whowechina/geki_pico/Production/3DPrint/geki_pico_lever_rotator_5mm.stl

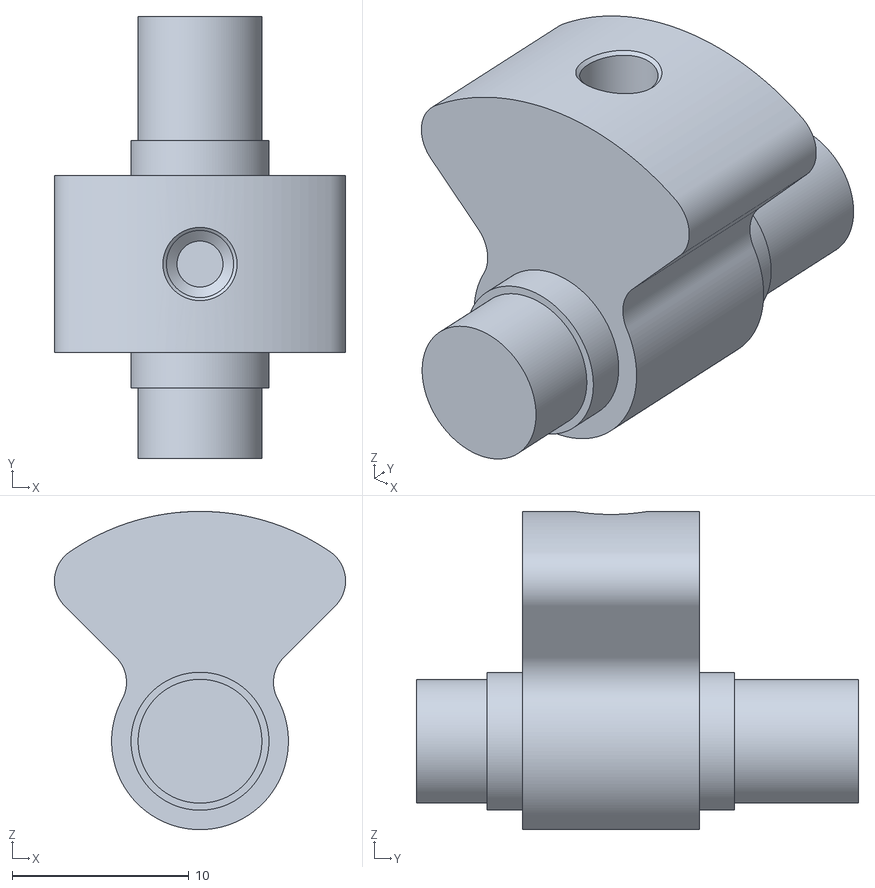
[picture p38: CAD file, 2024-10-14]
Production/3DPrint/geki_pico_lever_rotator_5mm.stl
16.5 x 25.0 x 18.0
