whowechina/geki_pico/PCB/main/3dmodels/SKPMAM.STEP

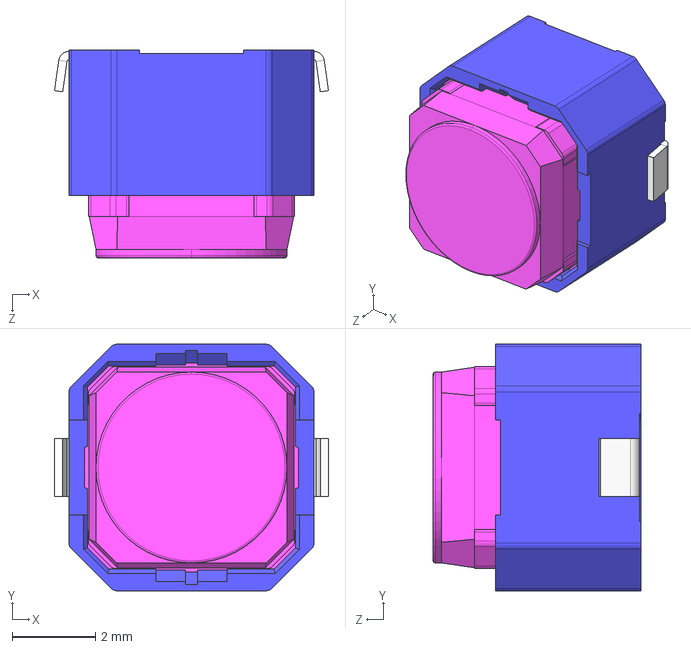
[picture p39: CAD file, 2023-09-29]
PCB/main/3dmodels/SKPMAM.STEP
6.60 x 5.94 x 5.00 mm
