whowechina/geki_pico/PCB/main/3dmodels/mpr121_breakout_v13.stl

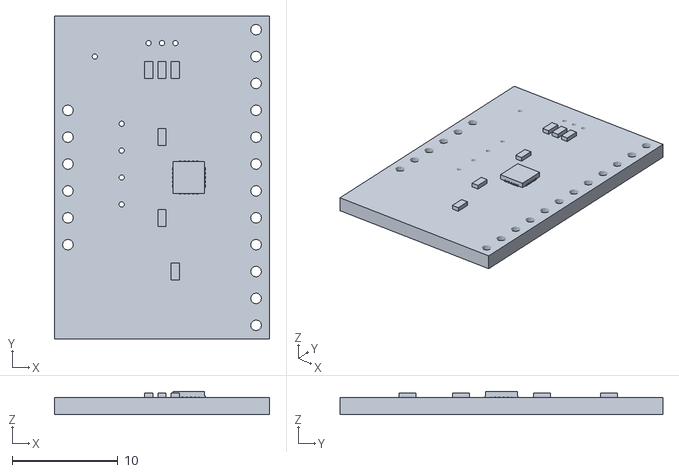
[picture p40: CAD file, 2023-09-29]
PCB/main/3dmodels/mpr121_breakout_v13.stl
20.3 x 30.5 x 2.20
