whowechina/geki_pico/Production/3DPrint/geki_pico_lever_fixer.stl

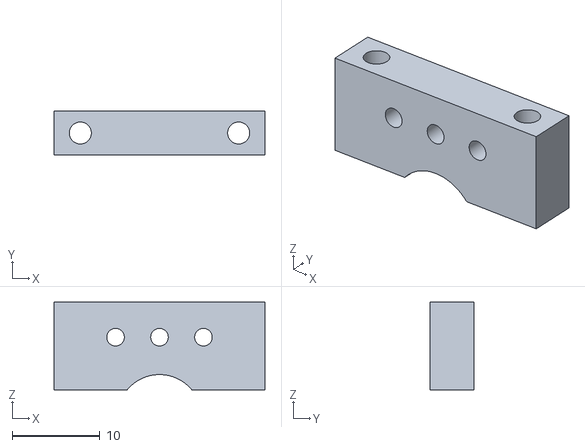
[picture p41: CAD file, 2024-10-14]
Production/3DPrint/geki_pico_lever_fixer.stl
24.0 x 5.00 x 10.0
