whowechina/geki_pico/Production/3DPrint/geki_pico_support_2_tof_no_cover.stl

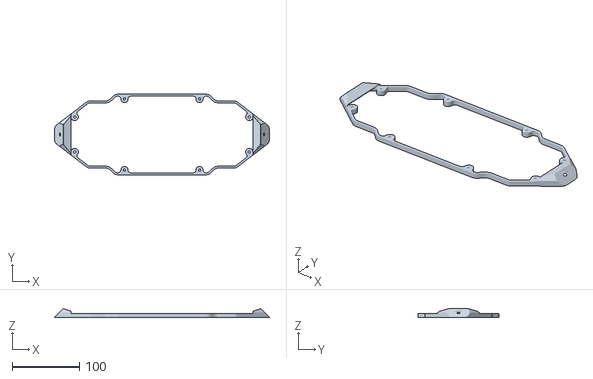
[picture p43: CAD file, 2024-09-18]
Production/3DPrint/geki_pico_support_2_tof_no_cover.stl
320.0 x 120.0 x 12.9
