whowechina/geki_pico/PCB/main/3dmodels/chu_keypad_lgp.step

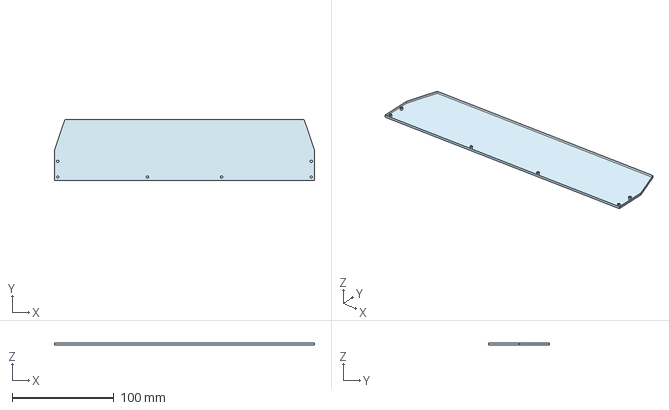
[picture p44: CAD file, 2023-09-29]
PCB/main/3dmodels/chu_keypad_lgp.step
256.0 x 60.0 x 2.00 mm
