whowechina/geki_pico/Production/3DPrint/geki_pico_button_aux.stl

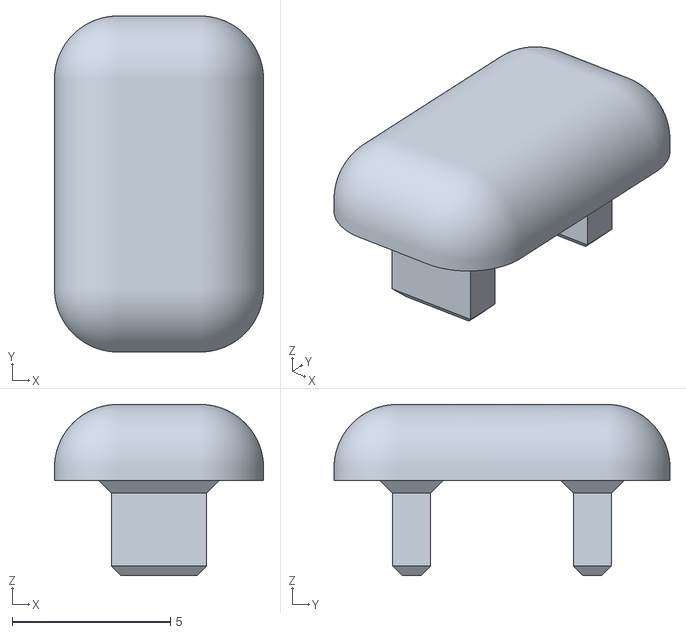
[picture p45: CAD file, 2024-09-17]
Production/3DPrint/geki_pico_button_aux.stl
6.60 x 10.6 x 5.40
