whowechina/geki_pico/PCB/main/3dmodels/Slider.step

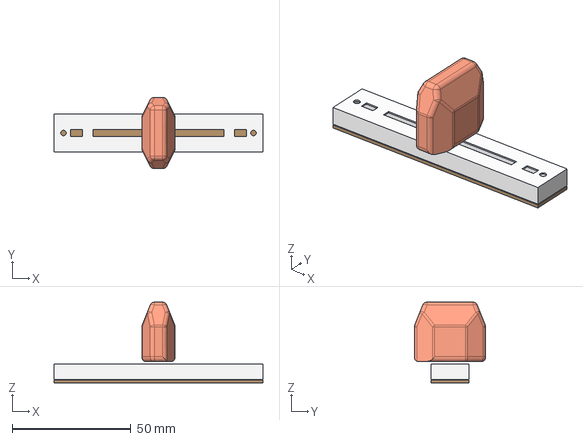
[picture p46: CAD file, 2023-09-29]
PCB/main/3dmodels/Slider.step
88.0 x 30.0 x 34.0 mm
