whowechina/geki_pico/PCB/main/3dmodels/Magnetic Pogo Connector 5 Pin (Type 3).STEP

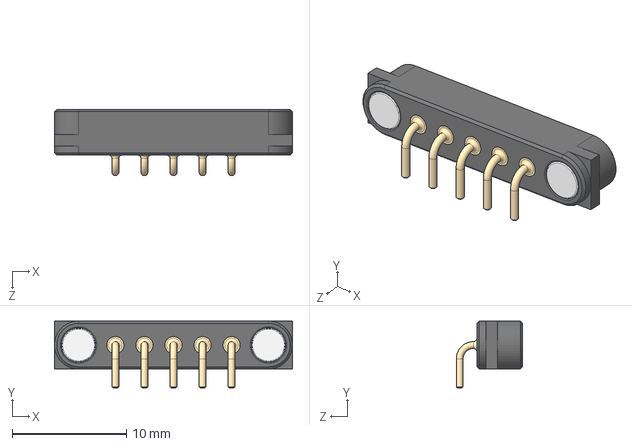
[picture p47: CAD file, 2023-09-29]
PCB/main/3dmodels/Magnetic Pogo Connector 5 Pin (Type 3).STEP
20.8 x 5.85 x 5.80 mm
