whowechina/geki_pico/Production/3DPrint/geki_pico_lever_base.stl

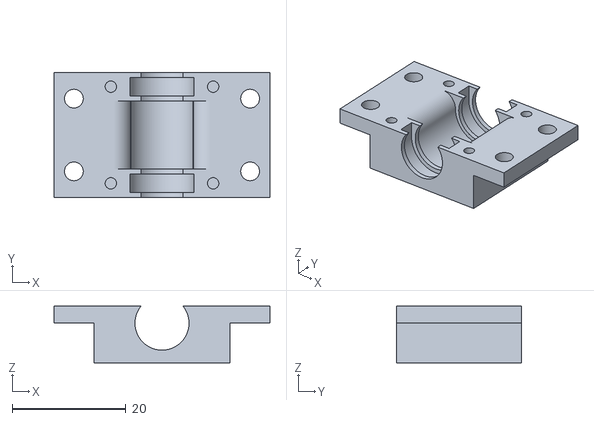
[picture p48: CAD file, 2024-09-17]
Production/3DPrint/geki_pico_lever_base.stl
38.0 x 22.0 x 10.0
