whowechina/geki_pico/PCB/main/3dmodels/gp2y0e03.3mf

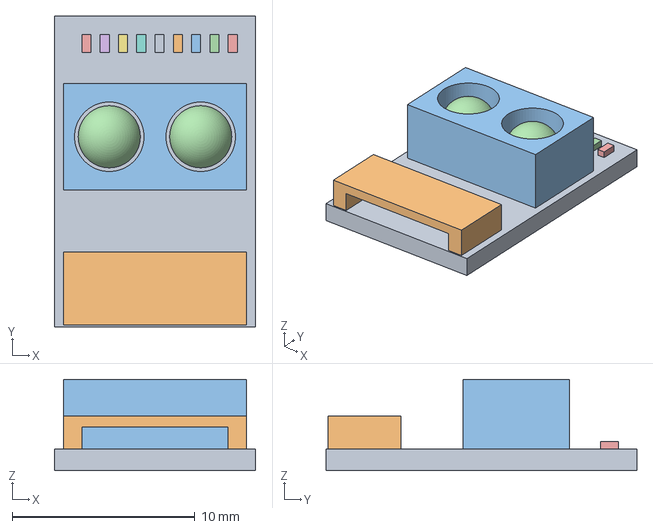
[picture p50: CAD file, 2023-09-29]
PCB/main/3dmodels/gp2y0e03.3mf
11.0 x 17.0 x 5.00 mm
