whowechina/geki_pico/PCB/main/3dmodels/Magnetic Pogo Connector 5 Pin (M) - 副本.STEP

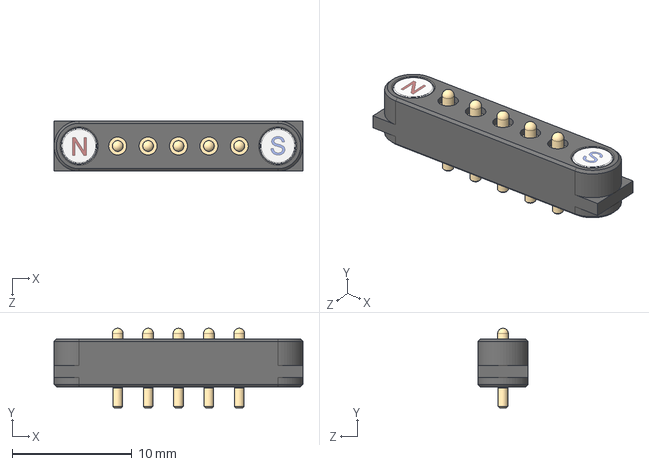
[picture p51: CAD file, 2023-09-29]
PCB/main/3dmodels/Magnetic Pogo Connector 5 Pin (M) - 副本.STEP
20.8 x 6.65 x 4.20 mm
