whowechina/geki_pico/PCB/main/3dmodels/EVQ-P1D05M.stp

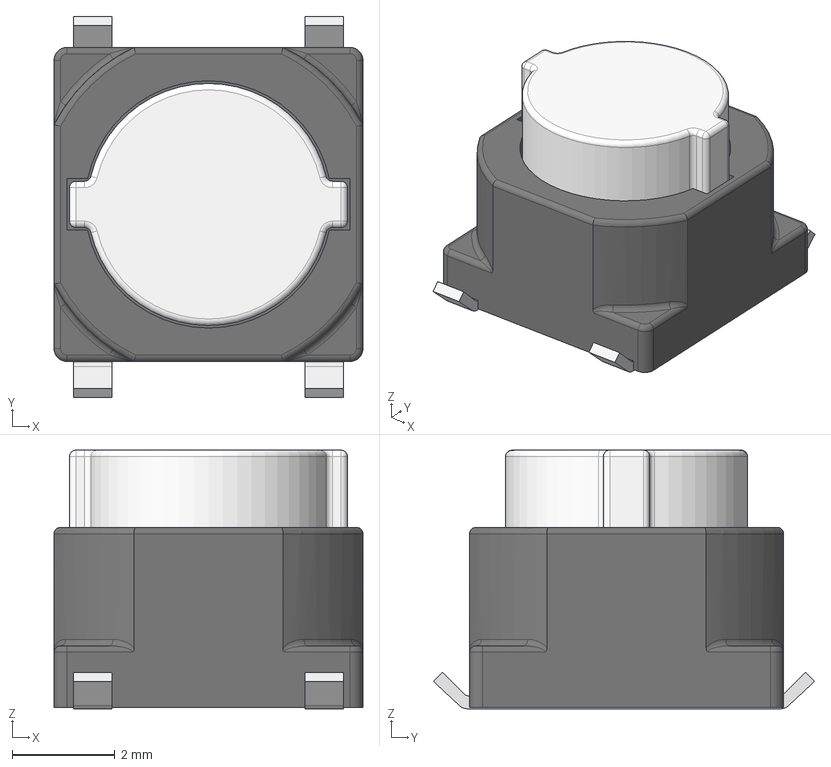
[picture p52: CAD file, 2023-09-29]
PCB/main/3dmodels/EVQ-P1D05M.stp
6.00 x 7.40 x 5.03 mm
