whowechina/geki_pico/PCB/main/3dmodels/keypad_lgp.3mf

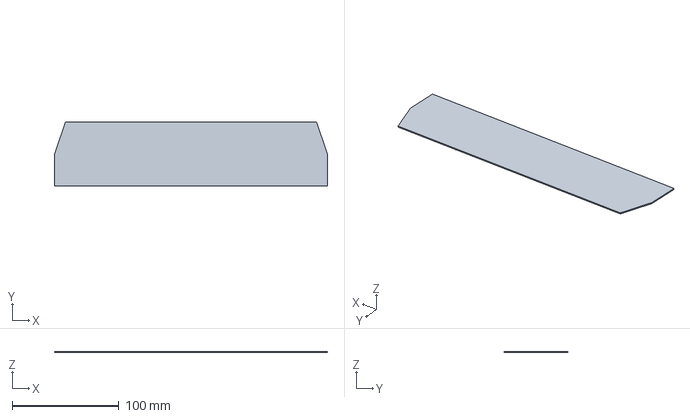
[picture p54: CAD file, 2023-09-29]
PCB/main/3dmodels/keypad_lgp.3mf
256.0 x 60.0 x 1.00 mm
