whowechina/geki_pico/firmware/src/wad_on_wav.h

const uint8_t wad_on[] = {189 , 9 , 0 , 0 , 128,126,127,127,127,127,126,127,126,126,127,126,127,127,127,124,123,124,122,124,126,126,123,125,124,125,124,124,125,123,123,123,122,123,123,124,124,123,122,120,121,121,121,122,120,121,121,121,120,120,
119,119,119,118,118,118,119,119,119,119,119,119,119,119,119,118,118,119,119,118,119,119,119,119,120,120,119,120,118,121,120,119,121,120,121,121,122,122,121,122,122,120,121,122,124,123,120,121,122,122,
122,121,121,121,121,120,120,119,119,121,122,128,119,132,129,128,130,127,124,124,126,137,127,118,124,126,130,122,129,125,125,120,122,120,126,127,124,127,130,129,129,130,132,131,129,129,134,134,136,127,
127,123,127,127,127,123,125,126,122,123,126,128,125,125,126,128,126,126,127,126,126,126,126,126,126,128,122,120,116,121,123,124,116,128,128,121,119,121,115,117,119,117,121,120,124,120,113,114,111,107,
109,112,110,108,110,108,104,103,103,101,102,101,102,99,99,99,98,98,97,97,97,96,97,95,96,94,95,93,94,93,93,92,92,92,92,92,92,92,92,91,90,92,91,91,91,90,92,90,92,92,
93,93,93,92,93,93,94,94,94,94,95,96,97,97,97,97,98,98,98,98,100,101,100,100,101,101,103,104,103,105,104,105,105,108,108,109,109,110,111,112,112,113,114,116,117,116,119,119,121,121,
123,123,124,125,126,126,128,130,131,131,133,131,133,134,136,137,137,137,136,149,150,144,140,145,153,147,143,149,149,150,152,155,154,153,152,156,154,159,159,161,160,162,162,163,163,164,165,166,166,166,
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
129,128,129,130,131,131,131,130,130,131,133,134,131,132,133,133,132,133,133,133,133,134,133,133,135,134,134,134,135,134,134,135,136,134,135,135,136,135,131,132,132,135,136,136,136,134,134,134,136,135,
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
