whowechina/geki_pico/firmware/src/wad_off_wav.h

const uint8_t wad_off[] ={159 , 4 , 0 , 0 , 119,135,131,118,123,133,131,128,118,134,124,125,125,124,138,124,125,132,118,139,119,136,130,114,139,128,124,135,129,122,125,127,134,123,140,114,134,127,118,141,124,129,119,134,117,138,127,119,141,111,
131,134,122,128,127,124,138,119,143,120,122,143,113,141,131,121,126,111,148,119,136,125,119,129,119,138,123,135,128,115,133,125,141,123,123,136,100,148,120,130,139,120,124,128,121,136,120,137,119,123,
127,123,141,121,129,115,130,130,129,133,127,121,127,122,136,130,117,129,112,128,124,135,133,112,141,114,133,124,123,135,118,138,111,126,131,121,138,116,119,133,125,134,132,116,137,104,139,125,126,130,
114,133,130,125,134,112,134,120,124,149,93,148,112,132,140,94,154,109,127,151,89,155,120,117,158,87,144,124,111,158,102,141,117,121,138,105,159,112,125,124,125,121,127,132,128,121,124,110,130,137,
122,142,122,114,130,122,127,128,121,137,103,135,122,116,135,115,146,110,138,129,110,151,113,122,128,109,145,106,139,131,97,146,103,131,126,110,150,102,131,122,133,140,105,105,147,101,133,142,100,150,
88,139,126,111,164,90,137,120,119,138,125,116,118,140,124,128,128,109,132,117,139,118,111,146,121,129,116,118,126,120,138,121,103,127,117,136,127,115,138,116,121,128,121,139,128,112,124,140,114,152,
110,126,121,122,134,121,145,102,120,141,103,160,106,122,138,103,160,92,162,109,103,140,116,127,136,100,153,100,126,142,100,159,104,109,152,82,161,105,136,127,97,161,66,173,124,114,136,93,152,105,
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
129,129,129,129,129,128,128,128,128,128,128,128,128,128,128,128,128,128,127,127,127,127,127,127,127,127,127,127,127,127,127,127,127,};
