whowechina/geki_pico/firmware/src/button.c

/*
 * Controller Buttons
 * WHowe <github.com/whowechina>
 * 
 */

#include "button.h"

#include <stdint.h>
#include <stdbool.h>
#include <string.h>

#include "hardware/gpio.h"
#include "hardware/timer.h"

#include "config.h"
#include "board_defs.h"

static const uint8_t button_gpio[] = BUTTON_DEF;

#define BUTTON_NUM (sizeof(button_gpio))

static bool sw_val[BUTTON_NUM]; /* true if pressed */
static uint64_t sw_freeze_time[BUTTON_NUM];
static uint32_t keydown_count[BUTTON_NUM];

void button_init()
{
    for (int i = 0; i < BUTTON_NUM; i++)
    {
        sw_val[i] = false;
        sw_freeze_time[i] = 0;
        int8_t gpio = button_gpio[i];
        gpio_init(gpio);
        gpio_set_function(gpio, GPIO_FUNC_SIO);
        gpio_set_dir(gpio, GPIO_IN);
        gpio_pull_up(gpio);
    }
}

uint8_t button_num()
{
    return BUTTON_NUM;
}

static uint16_t button_reading;

/* If a switch flips, it freezes for a while */
#define DEBOUNCE_FREEZE_TIME_US 20000
void button_update()
{
    static uint16_t old_buttons = 0;

    uint64_t now = time_us_64();
    uint16_t buttons = 0;

    for (int i = BUTTON_NUM - 1; i >= 0; i--) {
        bool sw_pressed = !gpio_get(button_gpio[i]);
        
        if (now >= sw_freeze_time[i]) {
            if (sw_pressed != sw_val[i]) {
                sw_val[i] = sw_pressed;
                sw_freeze_time[i] = now + DEBOUNCE_FREEZE_TIME_US;
            }
        }

        if (sw_val[i]) {
            buttons |= 1 << i;
            if ((old_buttons & (1 << i)) == 0) {
                keydown_count[i]++;
            }
        }
    }

	old_buttons = buttons;
    button_reading = buttons;
}

uint16_t button_read()
{
    return button_reading;
}

uint32_t button_stat_keydown(uint8_t id)
{
    if ((id < 0) || (id >= BUTTON_NUM)) {
        return 0;
    }

    uint32_t count = keydown_count[id];
    keydown_count[id] = 0;
    return count;
}

void button_clear_stat()
{
    memset(keydown_count, 0, sizeof(keydown_count));    
}
